MiguelDeTrool/Apeks/img/2_front.jpg

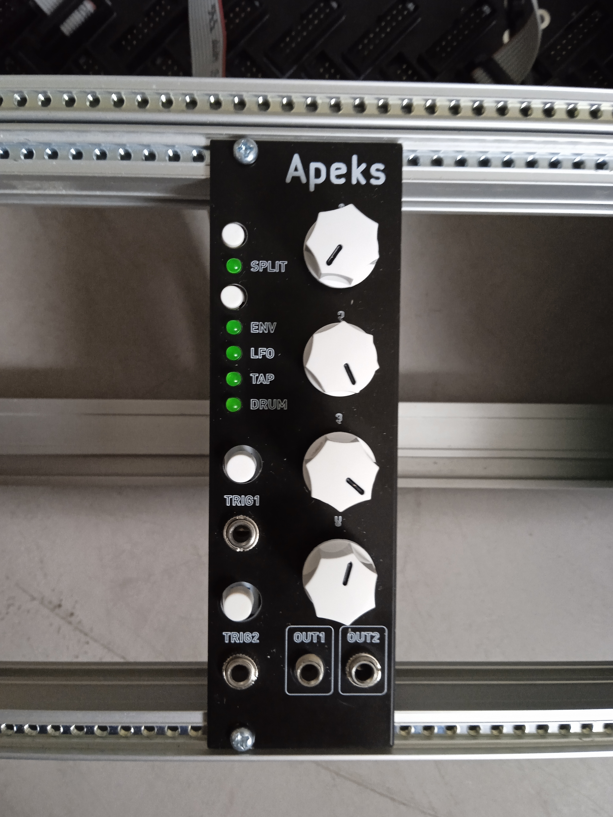
img/2_front.jpg
