MiguelDeTrool/Apeks/img/CP2102 wiring.png

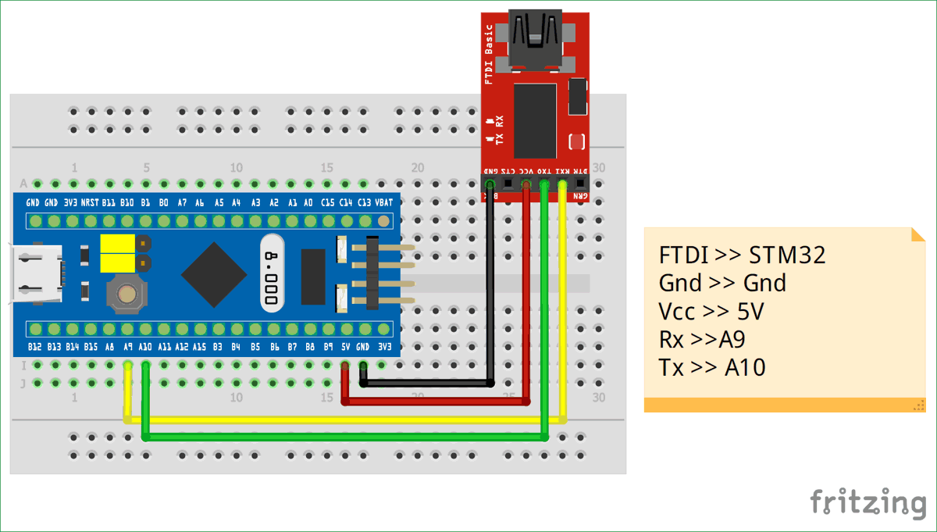
img/CP2102 wiring.png
