MiguelDeTrool/Apeks/firmware/peaks/modulations/lfo.h

// Copyright 2013 Emilie Gillet.
//
// Author: Emilie Gillet (emilie.o.gillet@gmail.com)
//
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
// See http://creativecommons.org/licenses/MIT/ for more information.
//
// -----------------------------------------------------------------------------
//
// LFO.

#ifndef PEAKS_MODULATIONS_LFO_H_
#define PEAKS_MODULATIONS_LFO_H_

#include "stmlib/stmlib.h"
#include "stmlib/algorithms/pattern_predictor.h"

#include "peaks/gate_processor.h"

namespace peaks {

enum LfoShape {
  LFO_SHAPE_SINE,
  LFO_SHAPE_TRIANGLE,
  LFO_SHAPE_SQUARE,
  LFO_SHAPE_STEPS,
  LFO_SHAPE_NOISE,
  LFO_SHAPE_LAST
};

class Lfo {
 public:
  typedef int16_t (Lfo::*ComputeSampleFn)();
   
  Lfo() { }
  ~Lfo() { }
  
  void Init();
  void Process(const GateFlags* gate_flags, int16_t* out, size_t size);
  
  void Configure(uint16_t* parameter, ControlMode control_mode) {
    if (control_mode == CONTROL_MODE_HALF) {
      if (sync_) {
        set_shape_integer(parameter[0]);
        set_parameter(parameter[1] - 32768);
      } else {
        set_rate(parameter[0]);
        set_shape_parameter_preset(parameter[1]);
      }
      set_reset_phase(0);
      set_level(65535);
    } else {
      if (sync_) {
        set_level(parameter[0]);
        set_shape_integer(parameter[1]);
        set_parameter(parameter[2] - 32768);
        set_reset_phase(parameter[3] - 32768);
      } else {
        set_level(65535);
        set_rate(parameter[0]);
        set_shape_integer(parameter[1]);
        set_parameter(parameter[2] - 32768);
        set_reset_phase(parameter[3] - 32768);
      }
    }
  }
  
  inline void set_rate(uint16_t rate) {
    rate_ = rate;
  }
  
  inline void set_shape(LfoShape shape) {
    shape_ = shape;
  }

  inline void set_shape_integer(uint16_t value) {
    shape_ = static_cast<LfoShape>(value * LFO_SHAPE_LAST >> 16);
  }
  
  void set_shape_parameter_preset(uint16_t value);
  
  inline void set_parameter(int16_t parameter) {
    parameter_ = parameter;
  }
  
  inline void set_reset_phase(int16_t reset_phase) {
    reset_phase_ = static_cast<int32_t>(reset_phase) << 16;
  }
  
  inline void set_sync(bool sync) {
    if (!sync_ && sync) {
      pattern_predictor_.Init();
    }
    sync_ = sync;
  }
  
  inline void set_level(uint16_t level) {
    level_ = level >> 1;
  }
  
 private:
  int16_t ComputeSampleSine();
  int16_t ComputeSampleTriangle();
  int16_t ComputeSampleSquare();
  int16_t ComputeSampleSteps();
  int16_t ComputeSampleNoise();
   
  uint16_t rate_;
  LfoShape shape_;
  int16_t parameter_;
  int32_t reset_phase_;
  int32_t level_;

  bool sync_;
  uint32_t sync_counter_;
  stmlib::PatternPredictor<32, 8> pattern_predictor_;
  
  uint32_t phase_;
  uint32_t phase_increment_;
  
  uint32_t period_;
  uint32_t end_of_attack_;
  uint32_t attack_factor_;
  uint32_t decay_factor_;
  int16_t previous_parameter_;
  
  int32_t value_;
  int32_t next_value_;
  
  static ComputeSampleFn compute_sample_fn_table_[];

  DISALLOW_COPY_AND_ASSIGN(Lfo);
};

}  // namespace peaks

#endif  // PEAKS_MODULATIONS_LFO_H_
